mike-rankin/ESP32_Round_CO2_Desktop_Sensor/Images/IMG_2840.jpg

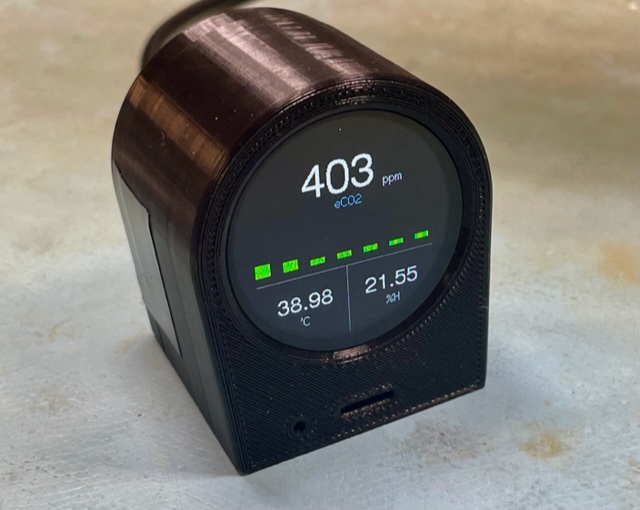
Images/IMG_2840.jpg
